CristianSusa/piano-allwinner-113/embedded-systems-development/images/devboard.png

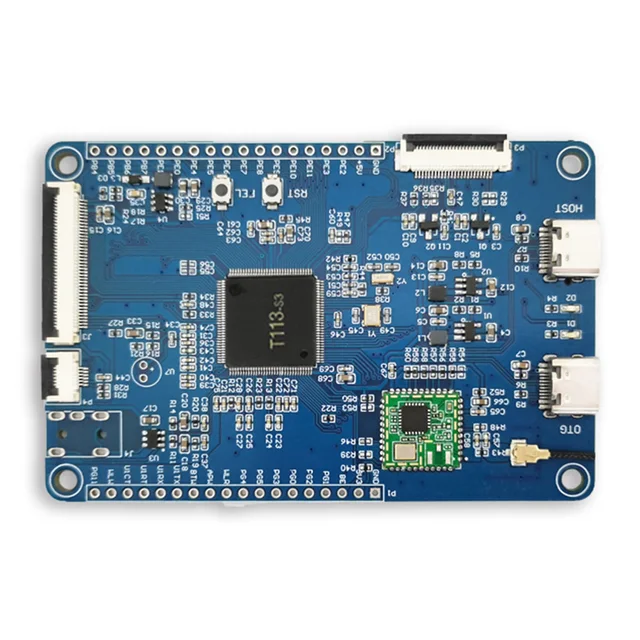
embedded-systems-development/images/devboard.png
